eigenein/one-wire-to-ntc/src/table.h

#ifndef NTC_TABLE_H_
#define NTC_TABLE_H_

const static float TABLE[] PROGMEM = {
    3148,  // #0000     0 0.0000°C R: 33252 V: 0.769
    3145,  // #0001     1 0.0625°C R: 33143 V: 0.768
    3143,  // #0002     2 0.1250°C R: 33034 V: 0.768
    3141,  // #0003     3 0.1875°C R: 32926 V: 0.767
    3138,  // #0004     4 0.2500°C R: 32818 V: 0.766
    3136,  // #0005     5 0.3125°C R: 32711 V: 0.766
    3133,  // #0006     6 0.3750°C R: 32604 V: 0.765
    3131,  // #0007     7 0.4375°C R: 32497 V: 0.765
    3128,  // #0008     8 0.5000°C R: 32391 V: 0.764
    3126,  // #0009     9 0.5625°C R: 32285 V: 0.764
    3124,  // #000A    10 0.6250°C R: 32180 V: 0.763
    3121,  // #000B    11 0.6875°C R: 32075 V: 0.762
    3119,  // #000C    12 0.7500°C R: 31970 V: 0.762
    3116,  // #000D    13 0.8125°C R: 31866 V: 0.761
    3114,  // #000E    14 0.8750°C R: 31762 V: 0.761
    3112,  // #000F    15 0.9375°C R: 31659 V: 0.760
    3109,  // #0010    16 1.0000°C R: 31555 V: 0.759
    3107,  // #0011    17 1.0625°C R: 31453 V: 0.759
    3104,  // #0012    18 1.1250°C R: 31350 V: 0.758
    3102,  // #0013    19 1.1875°C R: 31249 V: 0.758
    3099,  // #0014    20 1.2500°C R: 31147 V: 0.757
    3097,  // #0015    21 1.3125°C R: 31046 V: 0.756
    3094,  // #0016    22 1.3750°C R: 30945 V: 0.756
    3092,  // #0017    23 1.4375°C R: 30845 V: 0.755
    3089,  // #0018    24 1.5000°C R: 30745 V: 0.755
    3087,  // #0019    25 1.5625°C R: 30645 V: 0.754
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
    3160,  // #0FFB    -5 -0.3125°C R: 33803 V: 0.772
    3157,  // #0FFC    -4 -0.2500°C R: 33692 V: 0.771
    3155,  // #0FFD    -3 -0.1875°C R: 33581 V: 0.771
    3152,  // #0FFE    -2 -0.1250°C R: 33471 V: 0.770
    3150,  // #0FFF    -1 -0.0625°C R: 33361 V: 0.769
};

#endif
